ThunderSloth/mcc-csc202-lp-mspm0g3507-breakouts/docs/artifacts/3-term/docs/renders/CSC202_LP_MSPM0G3507_3TERM_BREAKOUT-bottom.png

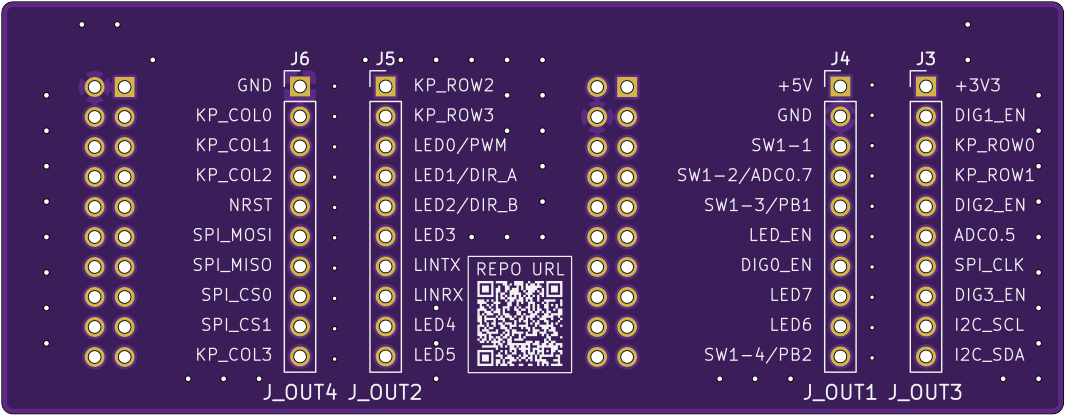
docs/artifacts/3-term/docs/renders/CSC202_LP_MSPM0G3507_3TERM_BREAKOUT-bottom.png
