ThunderSloth/mcc-csc202-lp-mspm0g3507-breakouts/docs/artifacts/dipsw-module/previews/fab-drawing.png

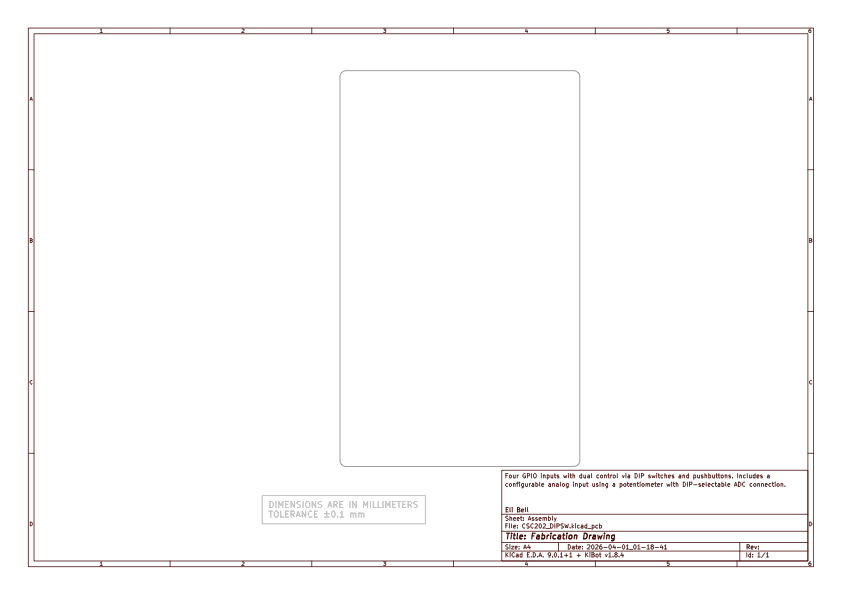
docs/artifacts/dipsw-module/previews/fab-drawing.png
