ThunderSloth/mcc-csc202-lp-mspm0g3507-breakouts/docs/artifacts/led-module/previews/fab-drawing.png

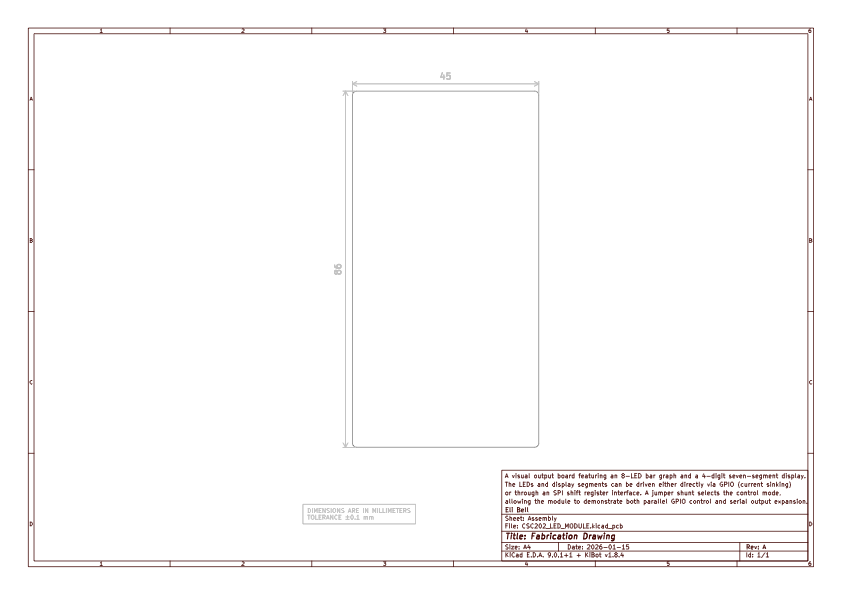
docs/artifacts/led-module/previews/fab-drawing.png
