ThunderSloth/mcc-csc202-lp-mspm0g3507-breakouts/docs/assets/repo_url_qr.png

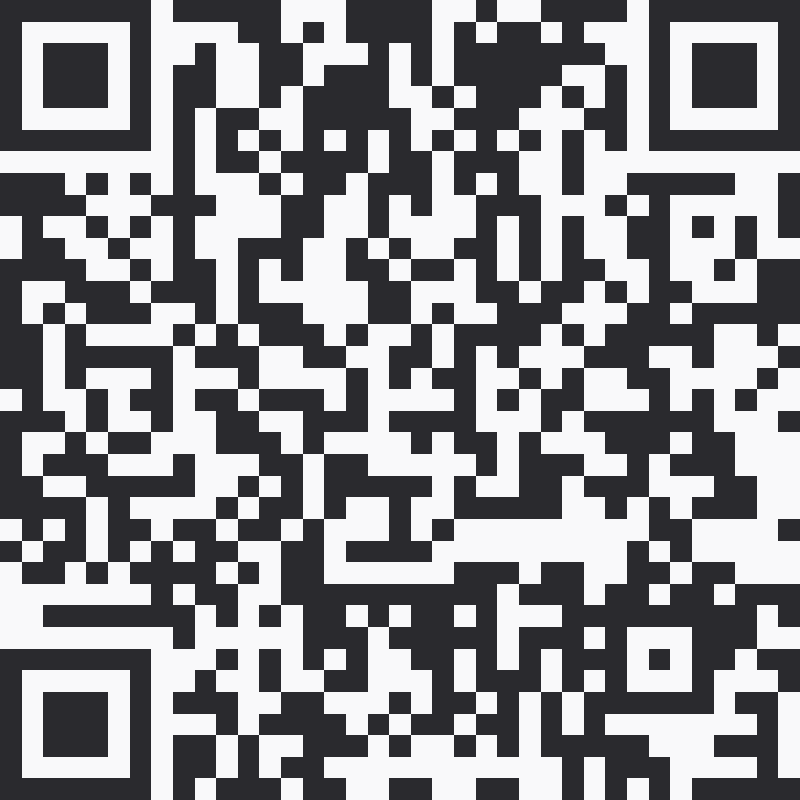
docs/assets/repo_url_qr.png
