ThunderSloth/mcc-csc202-lp-mspm0g3507-breakouts/docs/artifacts/2-term/previews/assembly-top.png

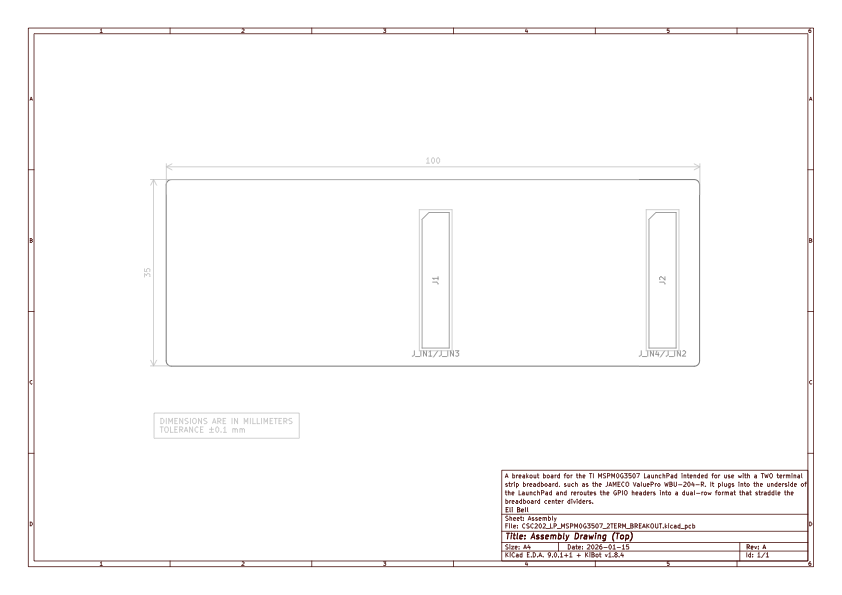
docs/artifacts/2-term/previews/assembly-top.png
