ThunderSloth/mcc-csc202-lp-mspm0g3507-breakouts/docs/artifacts/3-term/previews/assembly-top.png

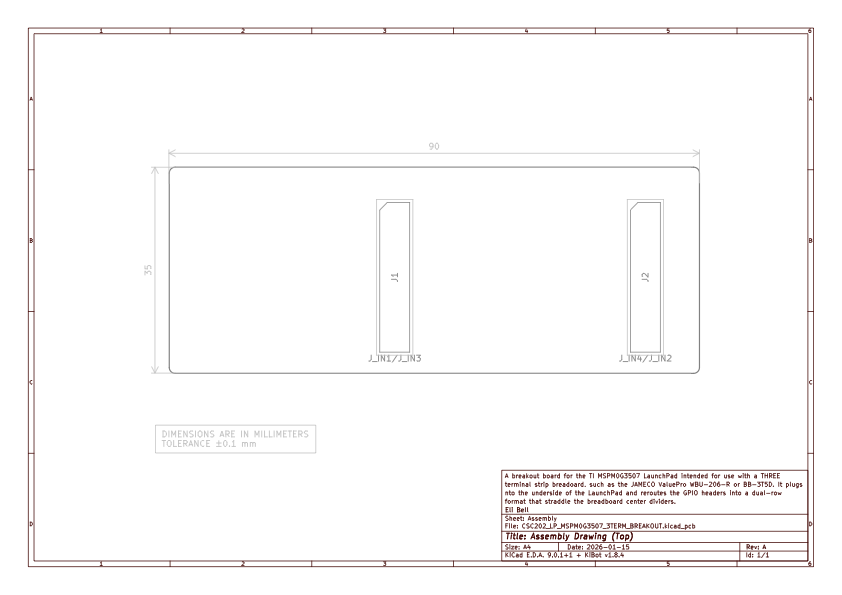
docs/artifacts/3-term/previews/assembly-top.png
