ThunderSloth/mcc-csc202-lp-mspm0g3507-breakouts/docs/artifacts/dipsw-module/previews/assembly-top.png

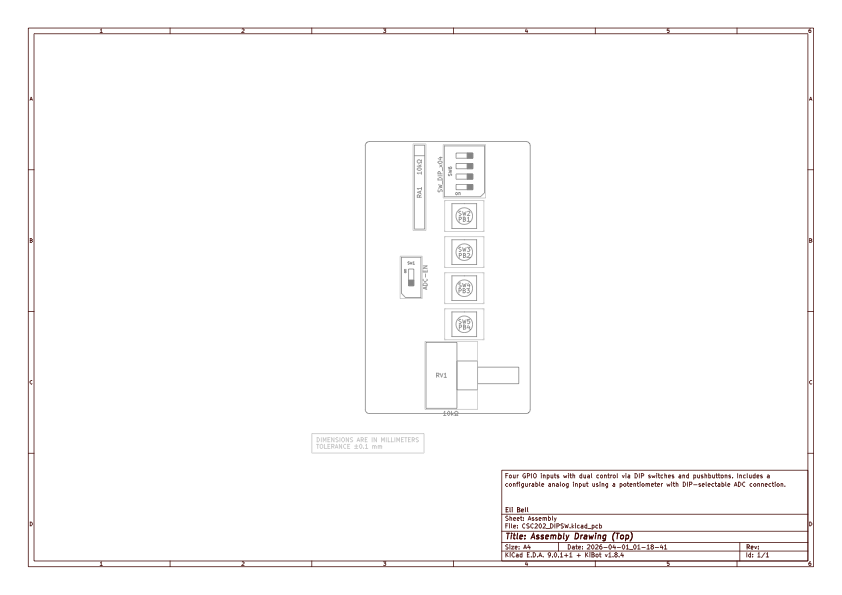
docs/artifacts/dipsw-module/previews/assembly-top.png
